cairanvanrooyen/rat_drone_synth/images/IMG_5051.jpeg

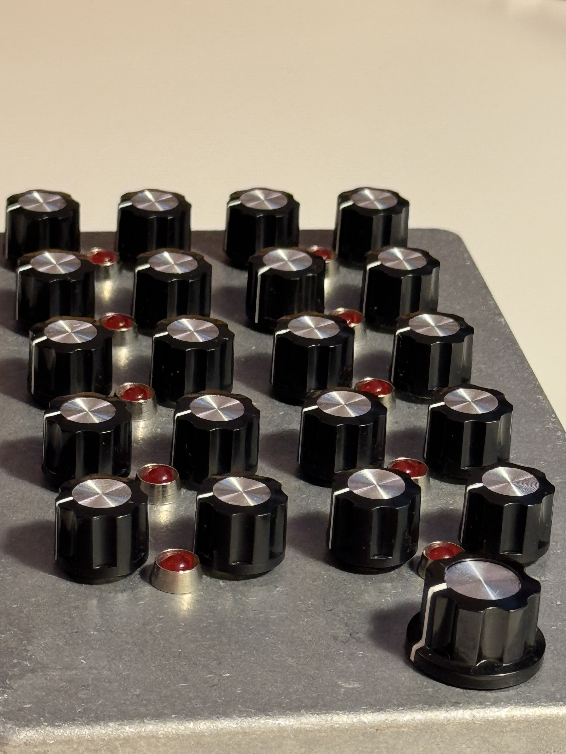
images/IMG_5051.jpeg
