cairanvanrooyen/rat_drone_synth/images/IMG_5052.jpeg

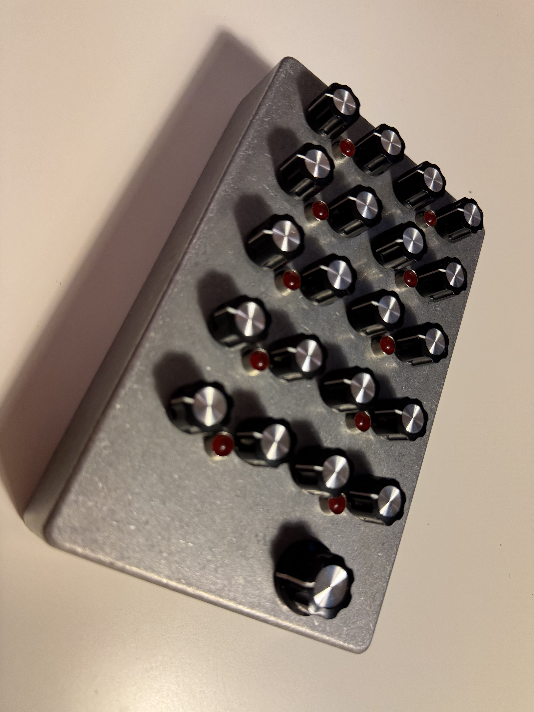
images/IMG_5052.jpeg
