cairanvanrooyen/rat_drone_synth/images/IMG_5071.jpeg

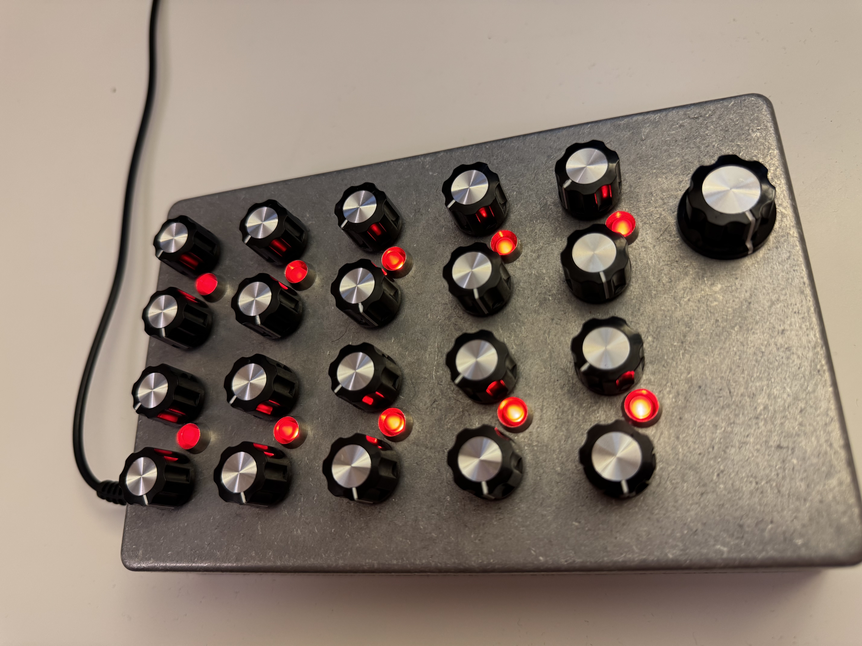
images/IMG_5071.jpeg
