cairanvanrooyen/rat_drone_synth/resources/2000_megadrone.jpg

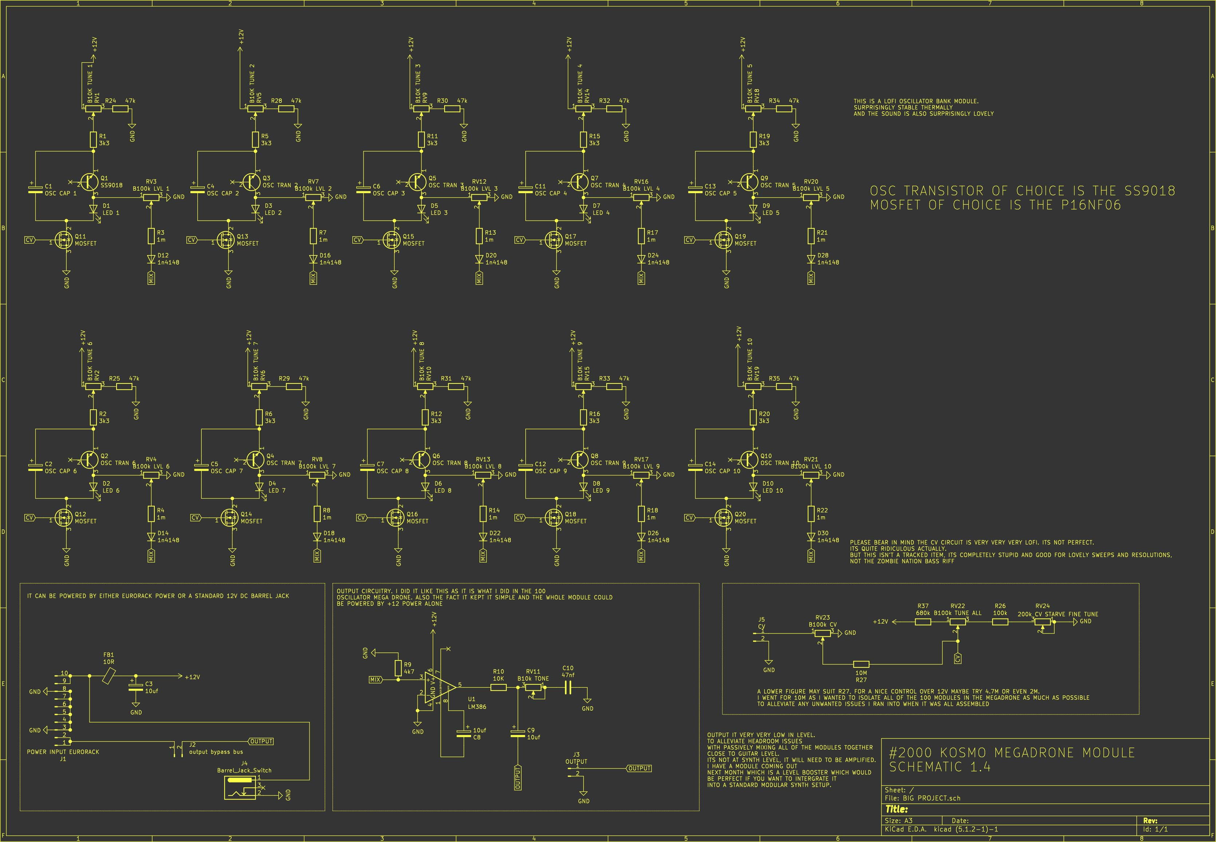
resources/2000_megadrone.jpg
