cairanvanrooyen/rat_drone_synth/resources/super_simple_osc.jpeg

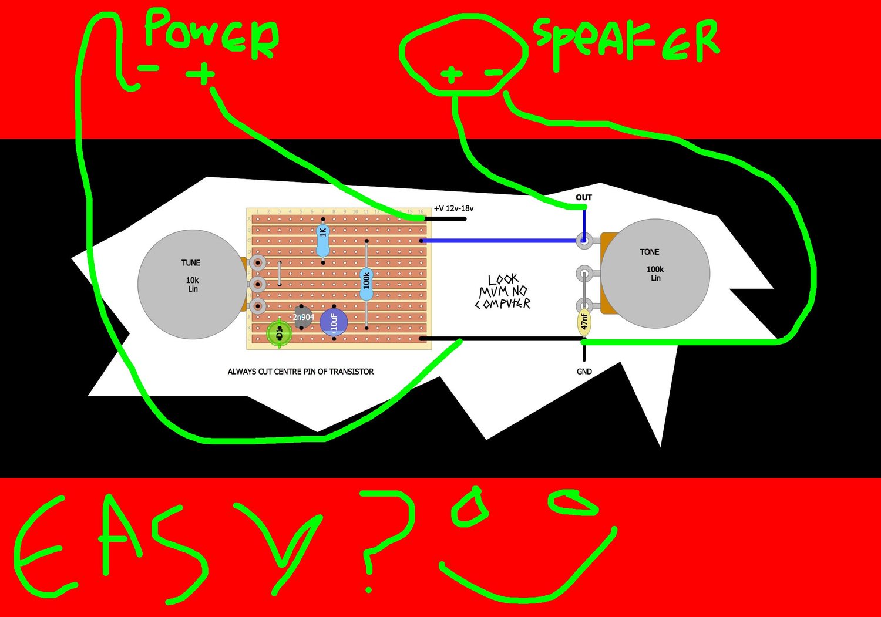
resources/super_simple_osc.jpeg
