cairanvanrooyen/rat_drone_synth/resources/super_simple_osc_bread.png

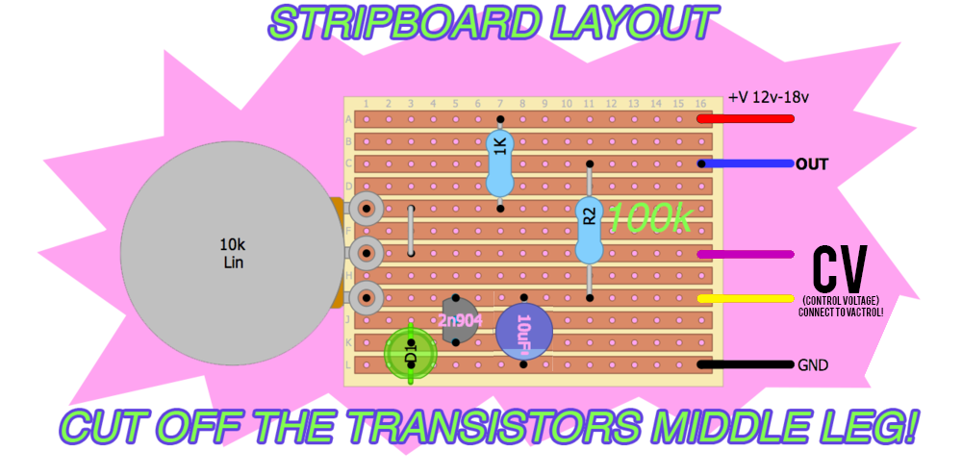
resources/super_simple_osc_bread.png
