cairanvanrooyen/rat_drone_synth/resources/super_simple_osc_sch.png

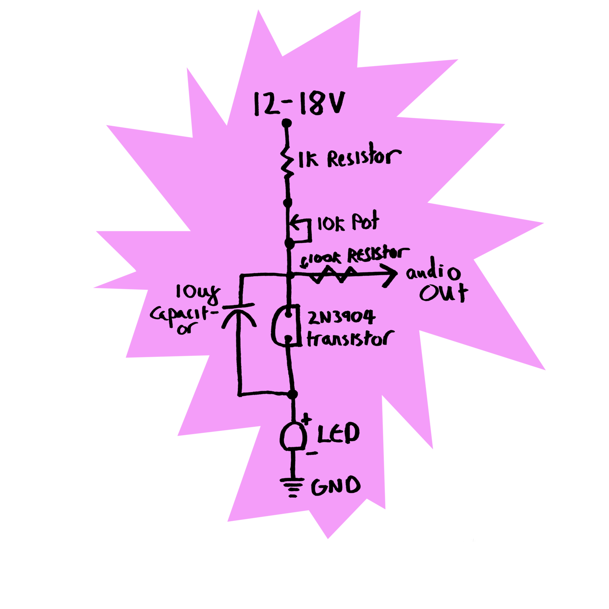
resources/super_simple_osc_sch.png
